TheDIYGuy999/RC_Transmitter_STM32/pong.h

/*
  A simple "1972 Atari Pong" game. Handy, if you crashed your RC car ;-)
  This code is based on: https://github.com/eholk/Arduino-Pong/blob/master/pong.ino
  Modified to use it with the u8glib and my "Micro RC" transmitter by TheDIYGuy999
*/

#ifndef pong_h
#define pong_h

#include "Arduino.h"

const uint8_t PADDLE_RATE = 5; // 15 5
const uint8_t BALL_RATE = 2; // 7 2
const uint8_t FRAME_RATE = 40; // Refresh display every 40ms = 25Hz (less slows the ball update down on a 72MHz MPU...)
const uint8_t PADDLE_HEIGHT = 14; // 14

const uint8_t half_paddle = PADDLE_HEIGHT / 2;

uint8_t ball_x = 64, ball_y = 32; // 64, 32
uint8_t ball_dir_x = -1, ball_dir_y = 1; // 1, 1

uint8_t new_x;
uint8_t new_y;

unsigned long ball_update;
unsigned long paddle_update;

const uint8_t CPU_X = 12; // 12
uint8_t cpu_y = 16;

const uint8_t PLAYER_X = 115; // 115
uint8_t player_y = 16;

uint8_t game_over_difference = 10; // The game is over after this point difference is reached!

uint8_t cpu_points = 0;
uint8_t player_points = 0;

boolean cpu_won = false;
boolean player_won = false;

//
// =======================================================================================================
// DISPLAY UPDATE SUBFUNCTION
// =======================================================================================================
//

void displayUpdate() {

  static unsigned long lastDisplay;
  if (millis() - lastDisplay >= FRAME_RATE) {
    lastDisplay = millis();

    // clear screen ----
    u8g2.clearBuffer();

    u8g2.drawFrame(0, 0, 128, 64);
    u8g2.drawPixel(new_x, new_y);
    /*u8g2.drawCircle(new_x, new_y, 1); // Ball
    u8g2.drawDisc(new_x + 10, new_y, 5); // Ball
    u8g2.drawDisc(new_x - 10, new_y, 5); // Ball
    u8g2.drawDisc(new_x, new_y + 10, 5); // Ball
    u8g2.drawDisc(new_x, new_y - 10, 5); // Ball
    u8g2.drawCircle(new_x, new_y, 20); // Ball*/
    u8g2.drawVLine(CPU_X, cpu_y, PADDLE_HEIGHT); // CPU paddle
    u8g2.drawVLine(PLAYER_X, player_y, PADDLE_HEIGHT); // Player paddle
    u8g2.drawVLine(64, 0, 3); // Vertical dashed line segments
    u8g2.drawVLine(64, 5, 3);
    u8g2.drawVLine(64, 10, 3);
    u8g2.drawVLine(64, 15, 3);
    u8g2.drawVLine(64, 20, 3);
    u8g2.drawVLine(64, 25, 3);
    u8g2.drawVLine(64, 30, 3);
    u8g2.drawVLine(64, 35, 3);
    u8g2.drawVLine(64, 40, 3);
    u8g2.drawVLine(64, 45, 3);
    u8g2.drawVLine(64, 50, 3);
    u8g2.drawVLine(64, 55, 3);
    u8g2.drawVLine(64, 60, 3);

    u8g2.setCursor(40, 10);  // CPU points counter
    u8g2.print(cpu_points);

    u8g2.setCursor(80, 10); // Player points counter
    u8g2.print(player_points);

    // Game over window
    if (cpu_won || player_won) {
      u8g2.setColorIndex(0);
      u8g2.drawBox(22, 12, 84, 45); // Clear area behind window
      u8g2.setColorIndex(1);
      u8g2.drawFrame(22, 12, 84, 45); // Draw window frame

      u8g2.setCursor(36, 28);
      u8g2.print("GAME OVER"); // Game over
      u8g2.setCursor(31, 48);
      u8g2.print("Press BACK!"); // Bress button "Back" to restart
    }
    if (cpu_won ) {
      u8g2.setCursor(38, 38);
      u8g2.print("YOU LOST"); // You lost
    }
    if (player_won ) {
      u8g2.setCursor(40, 38);
      u8g2.print("YOU WON"); // You won
    }

    // show display queue ----
    u8g2.sendBuffer();
  }
}

//
// =======================================================================================================
// PONG GAME
// =======================================================================================================
//

void pong() {
  unsigned long time = millis();

  static boolean center;

  // Restart game ----------------------------------------------------------
  if (digitalRead(BUTTON_BACK) == LOW) {
    cpu_won = false;
    player_won = false;
    cpu_points = 0;
    player_points = 0;
  }

  // Ball update -----------------------------------------------------------
  static unsigned long lastBall;
  if (millis() - lastBall >= BALL_RATE && !cpu_won && !player_won) {
    lastBall = millis();

    new_x = ball_x + ball_dir_x;
    new_y = ball_y + ball_dir_y;

    // Counter
    if (new_x > 54 && new_x < 74) center = true;
    if (center && new_x < CPU_X) player_points++, center = false; // Count CPU points
    if (center && new_x > PLAYER_X) cpu_points++, center = false; // Count Player points

    if (cpu_points - player_points >= game_over_difference) cpu_won = true; // Game over, you lost
    if (player_points - cpu_points >= game_over_difference) player_won = true; // Game over, you won

    // Check if we hit the vertical walls
    if (new_x == 1 || new_x == 126) {
      ball_dir_x = -ball_dir_x;
      new_x += ball_dir_x + ball_dir_x;
    }

    // Check if we hit the horizontal walls
    if (new_y == 1 || new_y == 62) {
      ball_dir_y = -ball_dir_y;
      new_y += ball_dir_y + ball_dir_y;
    }

    // Check if we hit the CPU paddle
    if (new_x == CPU_X
        && new_y >= cpu_y
        && new_y <= cpu_y + PADDLE_HEIGHT)
    {
      ball_dir_x = -ball_dir_x;
      new_x += ball_dir_x + ball_dir_x;
    }

    // Check if we hit the player paddle
    if (new_x == PLAYER_X
        && new_y >= player_y
        && new_y <= player_y + PADDLE_HEIGHT)
    {
      ball_dir_x = -ball_dir_x;
      new_x += ball_dir_x + ball_dir_x;
    }

    ball_x = new_x;
    ball_y = new_y;
  }

  // Paddle update -----------------------------------------------------------
  static unsigned long lastPaddle;
  if (millis() - lastPaddle >= PADDLE_RATE && !cpu_won && !player_won) {
    lastPaddle = millis();

    // CPU paddle control----
    if (cpu_y + half_paddle > ball_y) {
      cpu_y -= 1;
    }
    if (cpu_y + half_paddle < ball_y) {
      cpu_y += 1;
    }
    if (cpu_y < 1) cpu_y = 1;
    if (cpu_y + PADDLE_HEIGHT > 63) cpu_y = 63 - PADDLE_HEIGHT;

    // Player paddle control----
#ifdef CH2 // If we have a channel 2 (4 channel joystick transmitter)
    player_y = map(data.axis2, 100, 0, 0, (63 - PADDLE_HEIGHT));
#else // Else (2 channel car style transmitter)
    player_y = map(data.axis1, 100, 0, 0, (63 - PADDLE_HEIGHT));
#endif
    //player_y = map(analogRead(POT), 4095, 0, 0, (63 - PADDLE_HEIGHT));
  }

  // Display update ------------------------------------------------------------
  displayUpdate();
}

#endif
