TheDIYGuy999/RC_Transmitter_STM32/transmitterConfig.h

#ifndef transmitterConfig_h
#define transmitterConfig_h

#include "Arduino.h"

#define CONFIG_MICRO_RC // <- Select the correct transmitter configuration here before uploading!

//
// =======================================================================================================
// TRANSMITTEER SPECIFIC CONFIGURATIONS
// =======================================================================================================
//

// Configuration for the standard "Micro RC" transmitter with 4 channels and IR support----------------------
#ifdef CONFIG_MICRO_RC
// Battery type
const float cutoffVoltage = 4.4; // 4 x Eneloop cell
const float diodeDrop = 0.72;

// Channels, we have
#define CH1
#define CH2
#define CH3
#define CH4

// Infrared
boolean infrared = true;

// Board type
const float boardVersion = 1.0; // Board revision (MUST MATCH WITH YOUR BOARD REVISION!!)

// Joystick range (usually 4095)
// Some transmitters have a smaller mechanical working range. If so, define it here (from 600 to 1023)
int range = 4095;

#endif

// Configuration for a 2 channel transmitter with steering wheel. No IR support----------------------
#ifdef CONFIG_2_CH
// Battery type
const float cutoffVoltage = 4.4; // 4 x Eneloop cell
const float diodeDrop = 0.3;

// Channels, we have
#define CH1
#define CH3

// Infrared
boolean infrared = false;

// Board type
const float boardVersion = 1.1; // Board revision (MUST MATCH WITH YOUR BOARD REVISION!!)

// Joystick range (usually 4095)
// Some transmitters have a smaller mechanical working range. If so, define it here (from 2400 to 4095)
int range = 3282;

#endif



#endif
